FriedCircuits/USBMultimeter/STM32F429-Discovery-Prototype/Firmware/inc/widgetstyles.h

#ifndef _WIDGET_STYLES_H
#define _WIDGET_STYLES_H

#include "gfx.h"

// WidgetStyle: White
const GWidgetStyle white = {
	HTML2COLOR(0xFFFFFF),              // background
	HTML2COLOR(0x2A8FCD),              // focus

	// Enabled color set
	{
		HTML2COLOR(0x000000),         // text
		HTML2COLOR(0x404040),         // edge
		HTML2COLOR(0xE0E0E0),         // fill
		HTML2COLOR(0x00E000),         // progress (inactive area)
	},

	// Disabled color set
	{
		HTML2COLOR(0xC0C0C0),         // text
		HTML2COLOR(0x808080),         // edge
		HTML2COLOR(0xE0E0E0),         // fill
		HTML2COLOR(0xC0E0C0),         // progress (active area)
	},

	// Pressed color set
	{
		HTML2COLOR(0x404040),         // text
		HTML2COLOR(0x404040),         // edge
		HTML2COLOR(0x808080),         // fill
		HTML2COLOR(0x00E000),         // progress (active area)
	}
};

// WidgetStyle: Black
const GWidgetStyle black = {
	HTML2COLOR(0x000000),              // background
	HTML2COLOR(0x2A8FCD),              // focus

	// Enabled color set
	{
		HTML2COLOR(0xC0C0C0),         // text
		HTML2COLOR(0xC0C0C0),         // edge
		HTML2COLOR(0x606060),         // fill
		HTML2COLOR(0x008000),         // progress (inactive area)
	},

	// Disabled color set
	{
		HTML2COLOR(0x808080),         // text
		HTML2COLOR(0x404040),         // edge
		HTML2COLOR(0x404040),         // fill
		HTML2COLOR(0x004000),         // progress (active area)
	},

	// Pressed color set
	{
		HTML2COLOR(0xFFFFFF),         // text
		HTML2COLOR(0xC0C0C0),         // edge
		HTML2COLOR(0xE0E0E0),         // fill
		HTML2COLOR(0x008000),         // progress (active area)
	}
};

// WidgetStyle: syFCGreen
const GWidgetStyle syfcgreen = {
	HTML2COLOR(0x000000),              // background
	HTML2COLOR(0x000000),              // focus

	// Enabled color set
	{
		HTML2COLOR(0x43ec10),         // text
		HTML2COLOR(0x000000),         // edge
		HTML2COLOR(0x000000),         // fill
		HTML2COLOR(0x000000),         // progress (inactive area)
	},

	// Disabled color set
	{
		HTML2COLOR(0x000000),         // text
		HTML2COLOR(0x000000),         // edge
		HTML2COLOR(0x000000),         // fill
		HTML2COLOR(0x000000),         // progress (active area)
	},

	// Pressed color set
	{
		HTML2COLOR(0x008000),         // text
		HTML2COLOR(0x000000),         // edge
		HTML2COLOR(0x000000),         // fill
		HTML2COLOR(0x000000),         // progress (active area)
	}
};

// WidgetStyle: syBar
const GWidgetStyle sybar = {
	HTML2COLOR(0xa29ea2),              // background
	HTML2COLOR(0x000000),              // focus

	// Enabled color set
	{
		HTML2COLOR(0x000000),         // text
		HTML2COLOR(0x2f6bc8),         // edge
		HTML2COLOR(0x000000),         // fill
		HTML2COLOR(0x000000),         // progress (inactive area)
	},

	// Disabled color set
	{
		HTML2COLOR(0x000000),         // text
		HTML2COLOR(0x000000),         // edge
		HTML2COLOR(0x000000),         // fill
		HTML2COLOR(0x000000),         // progress (active area)
	},

	// Pressed color set
	{
		HTML2COLOR(0x000000),         // text
		HTML2COLOR(0x000000),         // edge
		HTML2COLOR(0x0ad639),         // fill
		HTML2COLOR(0x000000),         // progress (active area)
	}
};

// WidgetStyle: syBtn
const GWidgetStyle sybtn = {
	HTML2COLOR(0x000000),              // background
	HTML2COLOR(0x000000),              // focus

	// Enabled color set
	{
		HTML2COLOR(0x000000),         // text
		HTML2COLOR(0x000000),         // edge
		HTML2COLOR(0x000000),         // fill
		HTML2COLOR(0x000000),         // progress (inactive area)
	},

	// Disabled color set
	{
		HTML2COLOR(0x000000),         // text
		HTML2COLOR(0x000000),         // edge
		HTML2COLOR(0x000000),         // fill
		HTML2COLOR(0x000000),         // progress (active area)
	},

	// Pressed color set
	{
		HTML2COLOR(0x000000),         // text
		HTML2COLOR(0x000000),         // edge
		HTML2COLOR(0x000000),         // fill
		HTML2COLOR(0x000000),         // progress (active area)
	}
};


#endif /* _WIDGET_STYLES_H */
