FriedCircuits/USBMultimeter/STM32F429-Discovery-Prototype/Firmware/inc/colors.h

#ifndef _USER_COLORS_H
#define _USER_COLORS_H

#include "gfx.h"

#define white_studio HTML2COLOR(0xFFFFFF)
#define black_studio HTML2COLOR(0x000000)
#define gray_studio HTML2COLOR(0x808080)
#define blue_studio HTML2COLOR(0x0000FF)
#define red_studio HTML2COLOR(0xFF0000)
#define magenta_studio HTML2COLOR(0xFF00FF)
#define green_studio HTML2COLOR(0x008000)
#define yellow_studio HTML2COLOR(0xFFFF00)
#define cyan_studio HTML2COLOR(0x00FFFF)
#define lime_studio HTML2COLOR(0x00FF00)
#define maroon_studio HTML2COLOR(0x800000)
#define navy_studio HTML2COLOR(0x000080)
#define olive_studio HTML2COLOR(0x808000)
#define purple_studio HTML2COLOR(0x800080)
#define silver_studio HTML2COLOR(0xC0C0C0)
#define teal_studio HTML2COLOR(0x008080)
#define orange_studio HTML2COLOR(0xFFA500)
#define pink_studio HTML2COLOR(0xFFC0CB)
#define skyblue_studio HTML2COLOR(0x87CEEB)
#define _studio HTML2COLOR(0x43ec10)

#endif /* _USER_COLORS_H */
